iostwestcoast/radio_bot/Photos & Videoes/photo_2023-06-12_13-10-44.jpg

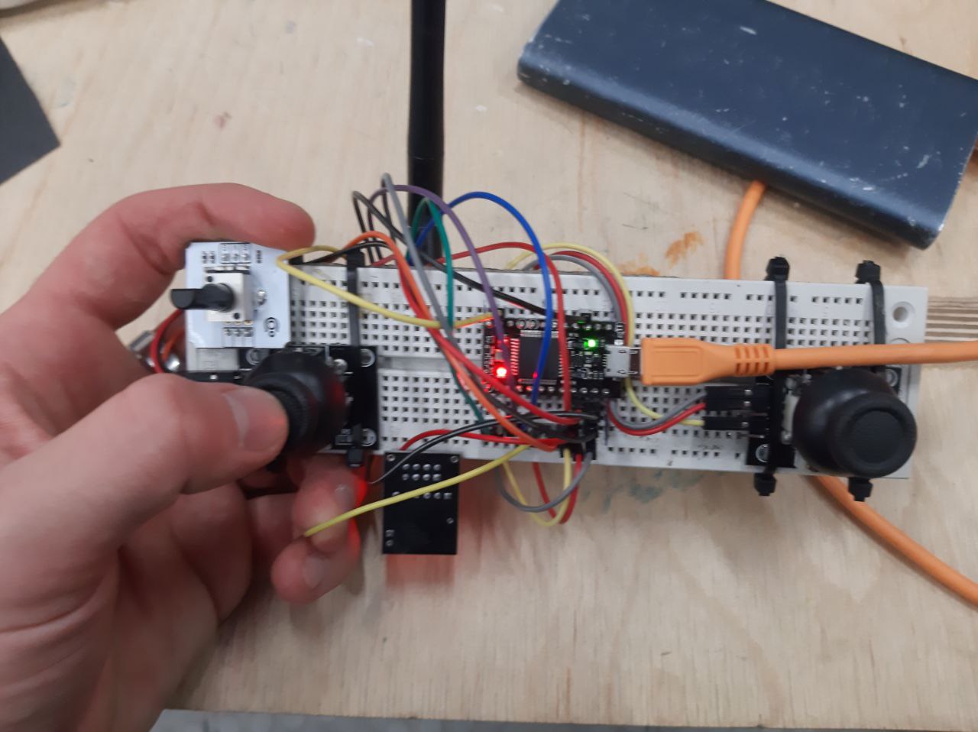
Photos & Videoes/photo_2023-06-12_13-10-44.jpg
