iostwestcoast/radio_bot/Photos & Videoes/photo_2023-06-12_13-11-36.jpg

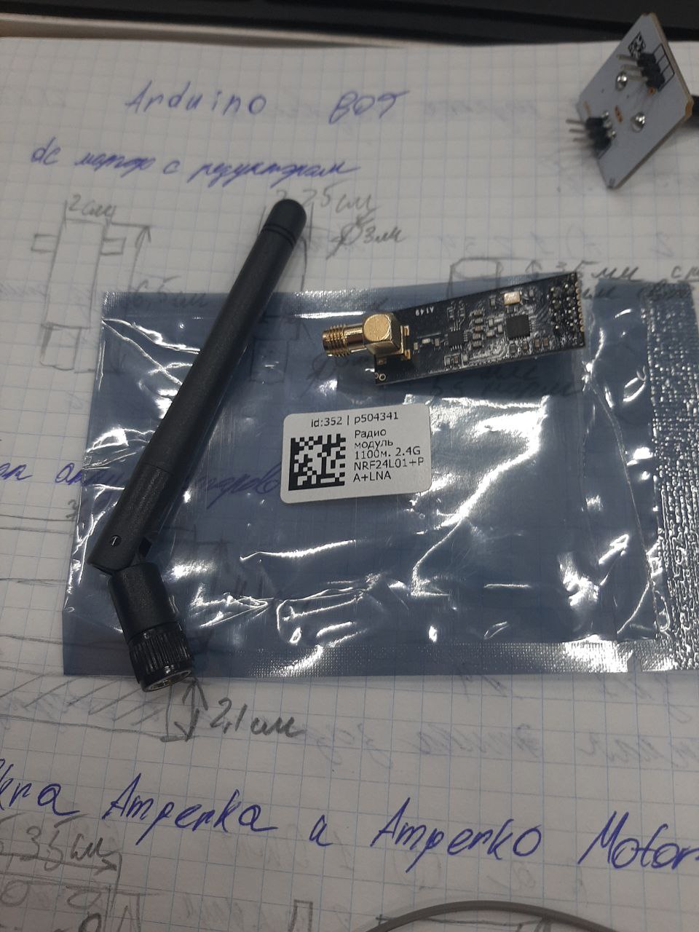
Photos & Videoes/photo_2023-06-12_13-11-36.jpg
