iostwestcoast/radio_bot/Photos & Videoes/photo_2023-06-13_16-50-43.jpg

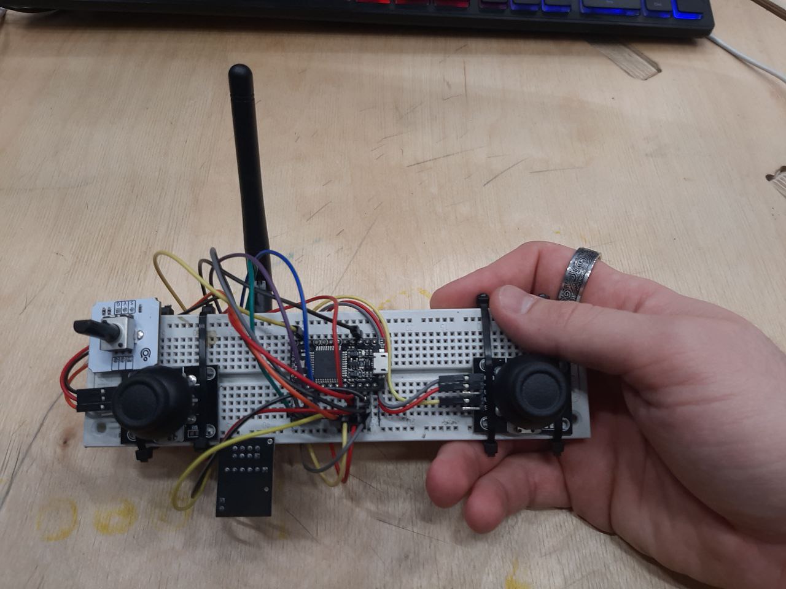
Photos & Videoes/photo_2023-06-13_16-50-43.jpg
