iostwestcoast/radio_bot/Photos & Videoes/photo_2023-06-13_16-50-44.jpg

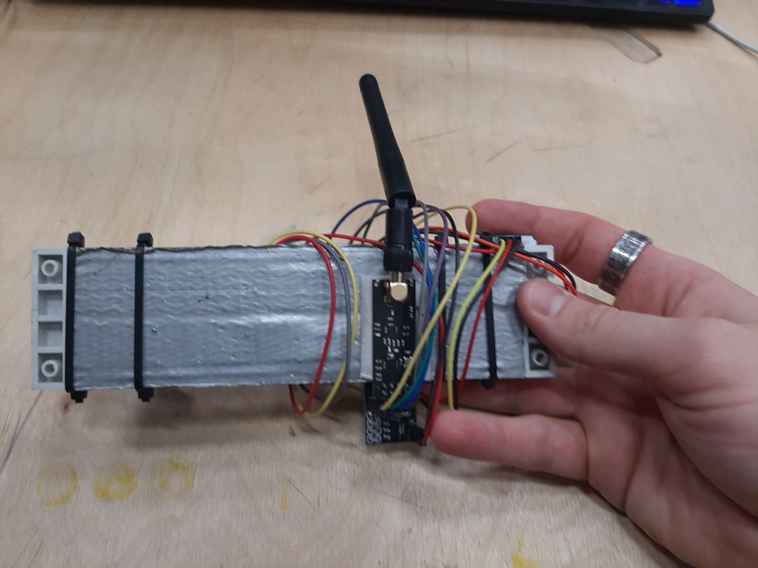
Photos & Videoes/photo_2023-06-13_16-50-44.jpg
