iostwestcoast/radio_bot/Photos & Videoes/photo_2023-06-13_16-51-02.jpg

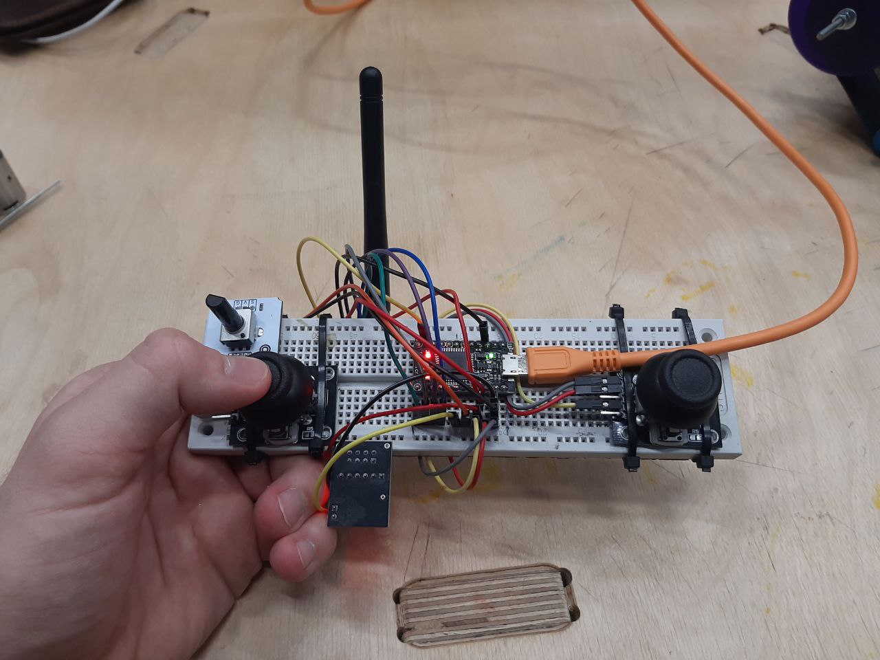
Photos & Videoes/photo_2023-06-13_16-51-02.jpg
