iostwestcoast/radio_bot/Photos & Videoes/photo_2023-06-13_16-51-12.jpg

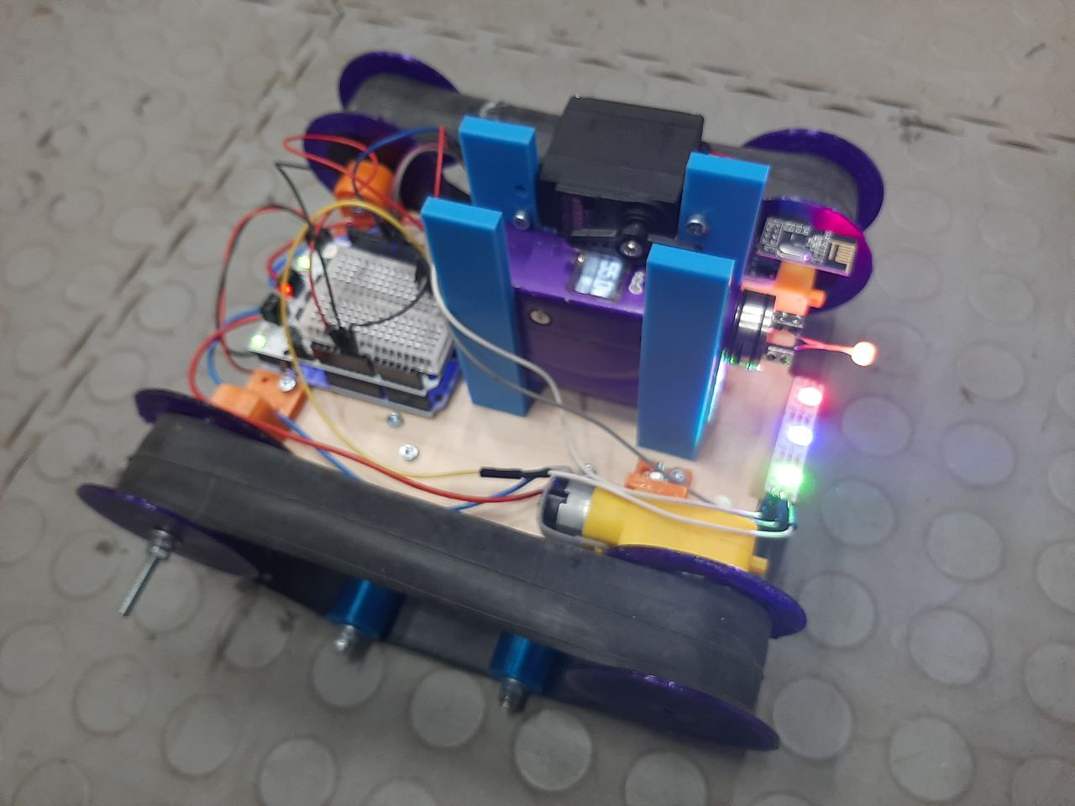
Photos & Videoes/photo_2023-06-13_16-51-12.jpg
